HakanD1/24v-to-5v-50w-buck-converter-stm32/Buck_converter_24Vto5V.asc

C1: cap; 10µ
D1: schottky; B540C
L1: ind; 33µ; Rser=1m
M1: nmos; IRF7468
R1: res; 0.5
V1: voltage; 24V
V2: voltage; PULSE(0 12 0 1n 1n 1.89u 8.33u)
Named nets: 0
.tran 0 10m 0 100n
